edgarkech/scalable_rollfilm_back/pre_OpenSCAD_version/STL/film_insert_v2.4.stl

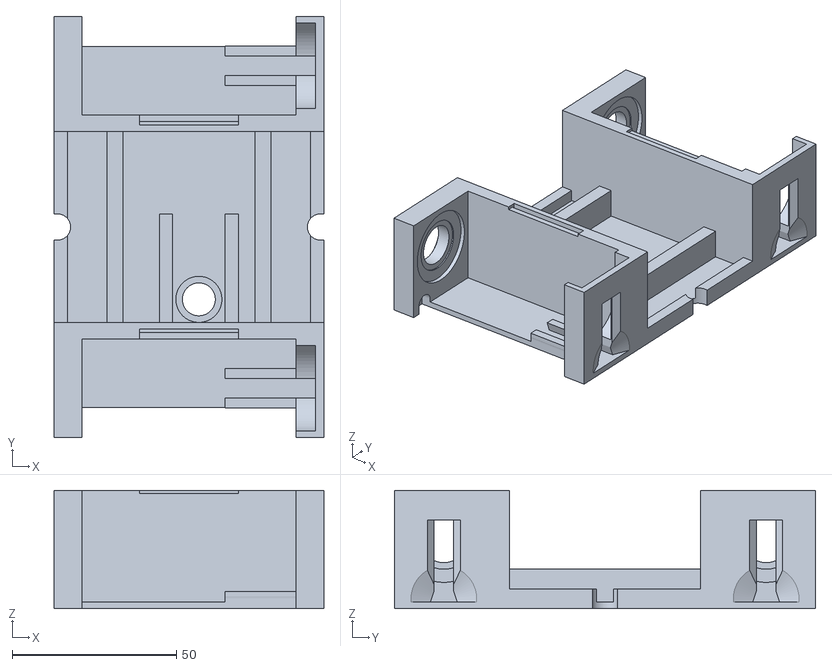
[picture p15: CAD file, 2022-03-08]
pre_OpenSCAD_version/STL/film_insert_v2.4.stl
82.0 x 128.0 x 36.0
