edgarkech/scalable_rollfilm_back/STL/cover.stl

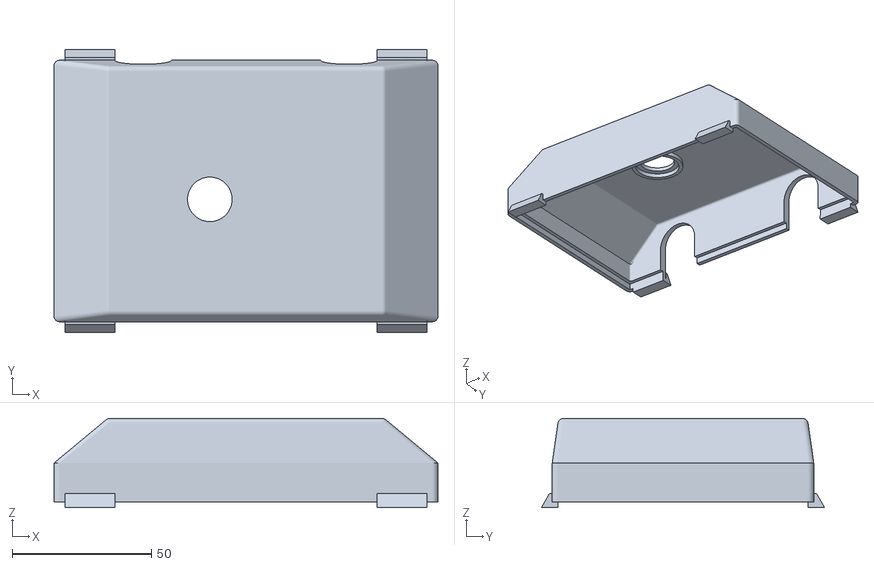
[picture p16: CAD file, 2024-03-24]
STL/cover.stl
138.0 x 101.8 x 32.0
