edgarkech/scalable_rollfilm_back/pre_OpenSCAD_version/STL/film_holder_bracket_v2.4.stl

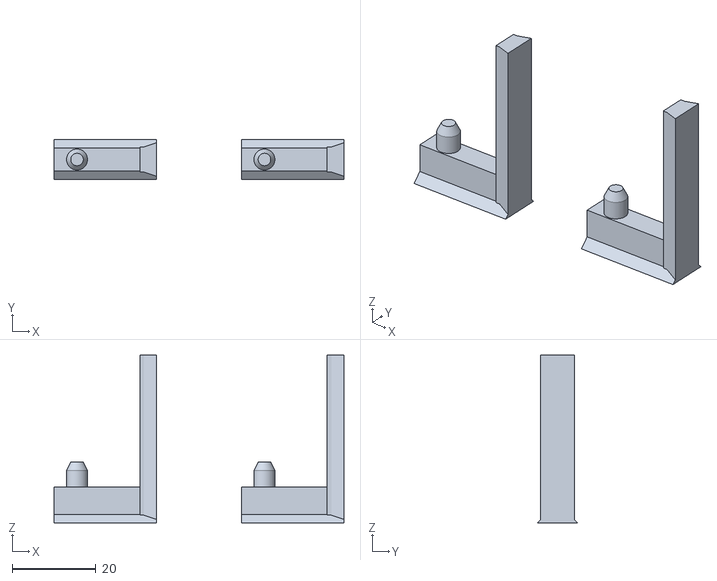
[picture p17: CAD file, 2022-03-08]
pre_OpenSCAD_version/STL/film_holder_bracket_v2.4.stl
69.2 x 9.60 x 40.0
