edgarkech/scalable_rollfilm_back/STL/baseplate_bottom.stl

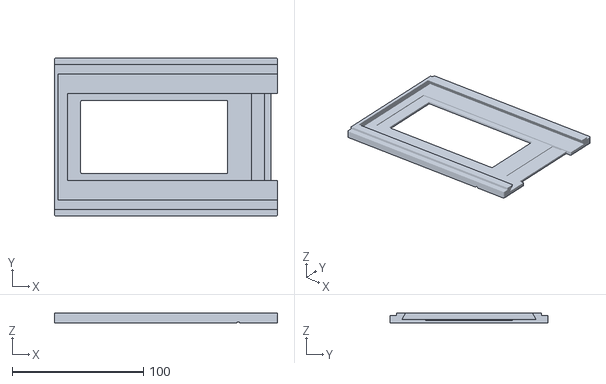
[picture p18: CAD file, 2024-03-18]
STL/baseplate_bottom.stl
170.0 x 120.5 x 8.00
