edgarkech/scalable_rollfilm_back/STL/baseplate_top.stl

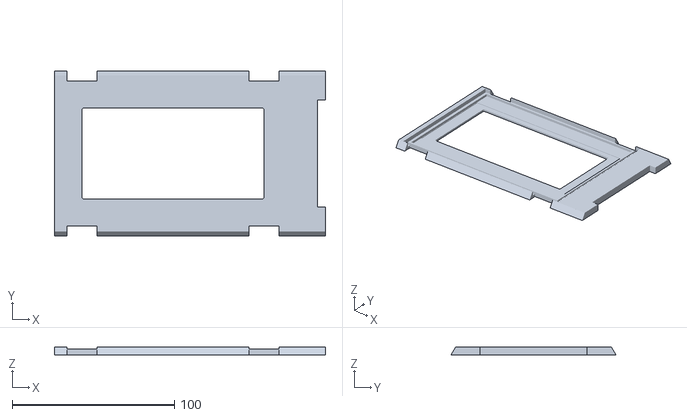
[picture p19: CAD file, 2024-03-18]
STL/baseplate_top.stl
167.0 x 101.8 x 5.01
