edgarkech/scalable_rollfilm_back/SCAD/baseplate_top.scad

// all includes are included in the assembly file, so no need do include them here (except temporarily for isolated part development)

// BOSL2 includes (https://github.com/revarbat/BOSL2/wiki)  
include <BOSL2/std.scad>
include <BOSL2/joiners.scad>

// including our configuration file
include <config.scad>;


// top plate 
union(){
    difference(){
        // top plate cutout
        translate([vTopplate_offsetX, vTopplate_offsetY, vTopplate_offsetZ])
        rotate([0,0,90])
    //    cube([vTopplateCutout_l, vTopplateCutout_w, vTopplateCutout_h]);
        dovetail("female", slide=vTopplate_l, width=vTopplate_w, height=vTopplate_h, angle=30);
        
        // film frame
        translate([vFilmframe_offsetX, vFilmframe_offsetY, vFilmframe_offsetZ])
        cuboid([vFilmframe_l, vFilmframe_w, vFilmframe_h], rounding=1, edges=[FRONT,LEFT,BACK,RIGHT], except=[TOP,BOT], p1=[0,0,0]);
        
        // film bed cutout
        translate([vFilmbedCutout_offsetX, vFilmbedCutout_offsetY, vFilmbedCutout_offsetZ])
        cube([vFilmbedCutout_l, vFilmbedCutout_w, vFilmbedCutout_h]);
        
        // film insert cutout
        translate([vFilmInsertCutout_offsetX, vFilmInsertCutout_offsetY, vFilmInsertCutout_offsetZ])
        cube([vFilmInsertCutout_l, vFilmInsertCutout_w, vFilmInsertCutout_h]);
           
        // dark slide grip cutout
        translate([vDarkSlideGripCutout_offsetX, vDarkSlideGripCutout_offsetY, vDarkSlideGripCutout_offsetZ])
        cube([vDarkSlideGripCutout_l+1, vDarkSlideGripCutout_w, vCassetteHeight+1]);
        
        // cover cutout
        translate([vCoverCutout_offsetX, vCoverCutout_offsetY, vCoverCutout_offsetZ])
        cube([vCoverCutout_l, vCoverCutout_w, vCoverCutout_h]);
        
        // claw cutouts
        translate([vCoverClawCutout_offsetX1, vCoverClawCutout_offsetY1, vCoverClawCutout_offsetZ])
        cube([vCoverClawCutout_l, vCoverClawCutout_w, vCoverClawCutout_h]);
        
        translate([vCoverClawCutout_offsetX2, vCoverClawCutout_offsetY1, vCoverClawCutout_offsetZ])
        cube([vCoverClawCutout_l, vCoverClawCutout_w, vCoverClawCutout_h]);
        
        translate([vCoverClawCutout_offsetX1, vCoverClawCutout_offsetY2, vCoverClawCutout_offsetZ])
        cube([vCoverClawCutout_l, vCoverClawCutout_w, vCoverClawCutout_h]);
        
        translate([vCoverClawCutout_offsetX2, vCoverClawCutout_offsetY2, vCoverClawCutout_offsetZ])
        cube([vCoverClawCutout_l, vCoverClawCutout_w, vCoverClawCutout_h]);
        
        
        
        
        // screw holes
        
    }
    // cover light seal
    translate([vCoverLightSeal_offsetX, vCoverLightSeal_offsetY, vCoverLightSeal_offsetZ])
    rect_tube(size=[vCoverLightSeal_l,vCoverLightSeal_w], wall=vCoverLightSeal_wall, h=vCoverLightSeal_h);
}
